wirahitaputramas/Weather-Station-ESP8266-PT-INTI-Internship/images/DHT22 Module.jpg

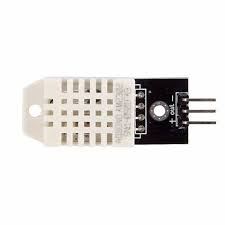
images/DHT22 Module.jpg
